sparkfun/SparkFun_UM980_Triband_GNSS_RTK_Breakout/docs/assets/3d_model/SparkFun_GNSS_UM980_3D_image.png

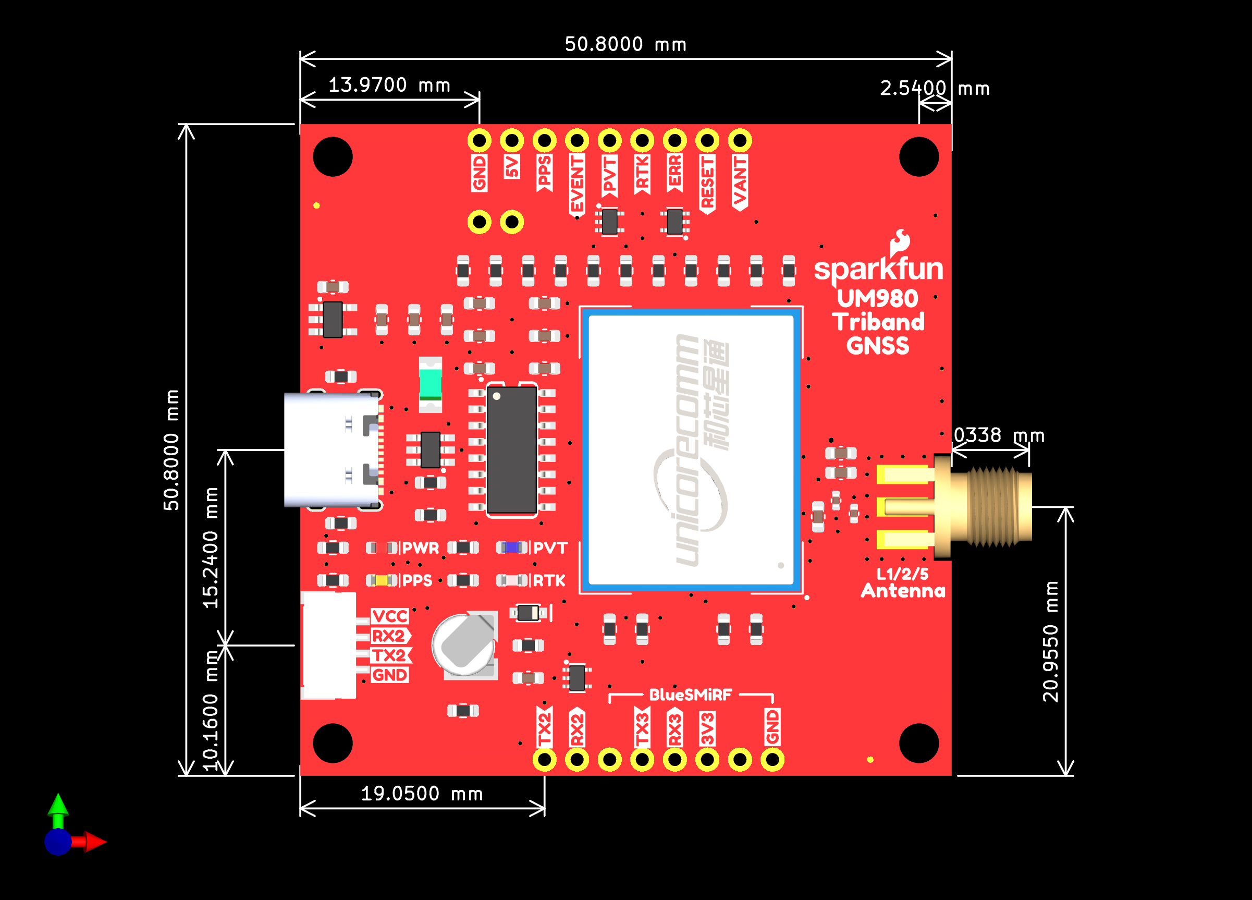
docs/assets/3d_model/SparkFun_GNSS_UM980_3D_image.png
