sparkfun/SparkFun_UM980_Triband_GNSS_RTK_Breakout/docs/assets/img/Arduino_Output_Ex_10_ESP32_Triband_GNSS_RTK_UM980.JPG

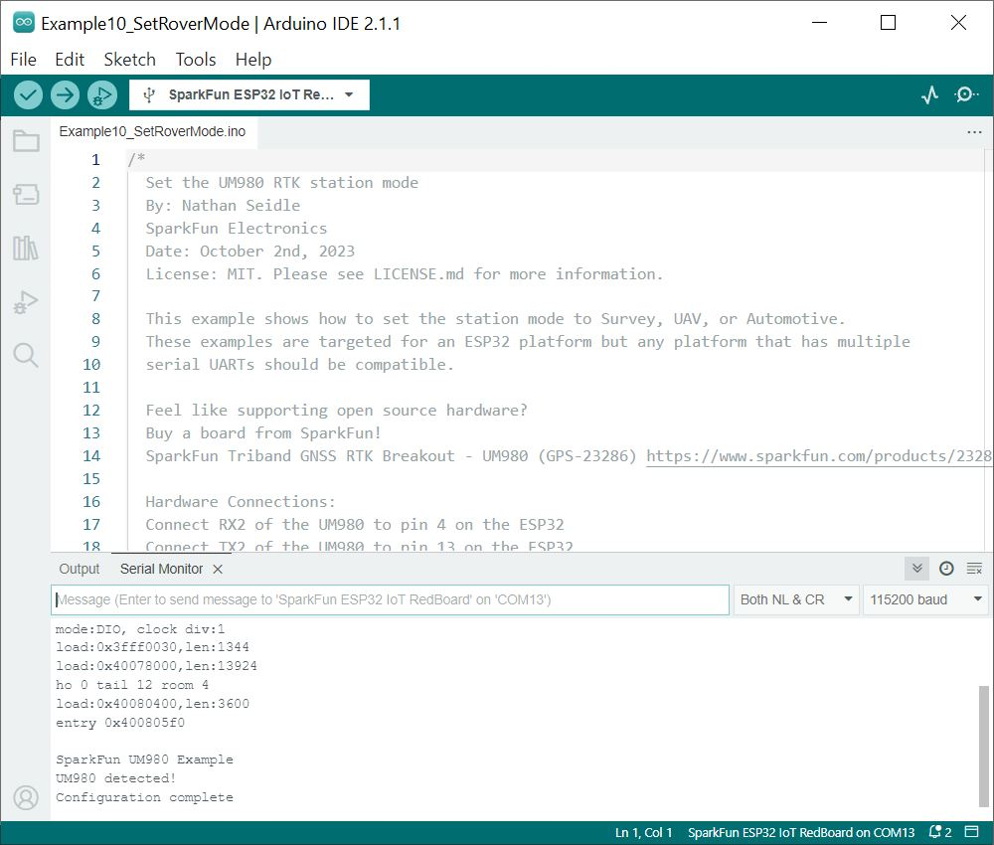
docs/assets/img/Arduino_Output_Ex_10_ESP32_Triband_GNSS_RTK_UM980.JPG
